softerhardware/Hermes-Lite/rtl/Hermes_Lite_CVA9.v

//
//  Hermes Lite Core Wrapper for BeMicro CV
// 
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
// (C) Steve Haynal KF7O 2014
//

module Hermes_Lite(
	input clk50mhz,
	input exp_present,
	input AD9866clk,
	input clk,
 	input extreset,
	output [7:0] leds,
	output exp_ptt_n,
	output [6:0] userout,
	input [2:0] dipsw,

    input cwkey_i,
    output cwkey_o,
    input ptt_i,

	// AD9866
	output [5:0] ad9866_pga,
`ifdef FULLDUPLEX
	input [5:0] ad9866_rx,
(* useioff = 1 *) output [5:0] ad9866_tx,
	input ad9866_rxsync,
	input ad9866_rxclk,
(* useioff = 1 *) output ad9866_txsync,
	output ad9866_txquietn,
`else
	inout [11:0] ad9866_adio,
	output ad9866_rxen,
	output ad9866_rxclk,
	output ad9866_txen,
	output ad9866_txclk,
`endif
	output ad9866_sclk,
    output ad9866_sdio,
    input  ad9866_sdo,
    output ad9866_sen_n,
    output ad9866_rst_n,
    output ad9866_mode,
   
    // MII Interface
  	output [3:0]PHY_TX,
  	output PHY_TX_EN,              
  	output  PHY_TX_CLOCK_out,           
  	input  [3:0]PHY_RX,     
  	input  RX_DV,                  
  	input  PHY_RX_CLOCK,           
  	output PHY_RESET_N,
	inout  PHY_MDIO,               
	output PHY_MDC,

	//12 bit adc's (ADC78H90CIMT)
	output ADCMOSI,                
	output ADCCLK,
 	input  ADCMISO,
	output nADCCS
);

// PARAMETERS

// Ethernet Interface
// 5c release, 4a testing
parameter MAC = {8'h00,8'h1c,8'hc0,8'ha2,8'h22,8'hdd};
parameter IP = {8'd0,8'd0,8'd0,8'd0};

// Clock Frequency
//parameter CLK_FREQ = 61440000;
parameter CLK_FREQ = 73728000;

// Number of Receivers
parameter NR = 3; // number of receivers to implement

parameter GIGABIT = 1;



// Clocks
wire IF_clk;
wire slowclk;
wire testAD9866clk;
wire AD9866clkX1;
wire IF_locked;
ifclocks_cv ifclocks_cv_inst(
	.refclk(clk),
	.rst(1'b0),
	.outclk_0(IF_clk),
	.outclk_1(testAD9866clk),
	.outclk_2(slowclk),
	.locked(IF_locked)
	);

// PLL clk must me on input 2 or 3
clkmux_cv clkmux (
	.inclk0x(AD9866clk),
	.inclk1x(AD9866clk),
	.inclk2x(testAD9866clk),
	.clkselect({~dipsw[2],1'b0}),
	.outclk(AD9866clkX1)
);

// Hermes Lite Core
hermes_lite_core #(
	.MAC(MAC),
	.IP(IP),
	.CLK_FREQ(CLK_FREQ),
	.NR(NR),
	.GIGABIT(GIGABIT)
	) 

	hermes_lite_core_inst(
	.clk50mhz(clk50mhz),
	.exp_present(dipsw[2]),
	.AD9866clkX1(AD9866clkX1),

	.IF_clk(IF_clk),
	.ad9866spiclk(IF_clk),
	.rstclk(slowclk),
	.EEPROM_clock(slowclk),
	.IF_locked(IF_locked),

 	.extreset(extreset),
	.leds(leds), 
	.exp_ptt_n(exp_ptt_n),
	.userout(userout),
	.dipsw(dipsw),

	.cwkey_i(cwkey_i),
	.cwkey_o(cwkey_o),

	.ptt_i(ptt_i),

	// AD9866
	.ad9866_pga(ad9866_pga),
`ifdef FULLDUPLEX
	.ad9866_tx(ad9866_tx),
	.ad9866_rx(ad9866_rx),
	.ad9866_rxsync(ad9866_rxsync),
	.ad9866_rxclk(ad9866_rxclk),
	.ad9866_txsync(ad9866_txsync),
	.ad9866_txquietn(ad9866_txquietn),
`else
	.ad9866_adio(ad9866_adio),
	.ad9866_rxen(ad9866_rxen),
	.ad9866_rxclk(ad9866_rxclk),
	.ad9866_txen(ad9866_txen),
	.ad9866_txclk(ad9866_txclk),
`endif
	.ad9866_sclk(ad9866_sclk),
    .ad9866_sdio(ad9866_sdio),
    .ad9866_sdo(ad9866_sdo),
    .ad9866_sen_n(ad9866_sen_n),
    .ad9866_rst_n(ad9866_rst_n),
    .ad9866_mode(ad9866_mode),
   
    // MMI Ethernet PHY
  	.PHY_TX(PHY_TX),
  	.PHY_TX_EN(PHY_TX_EN),        
  	.PHY_TX_CLOCK(1'b0),
  	.PHY_TX_CLOCK_out(PHY_TX_CLOCK_out),
  	.PHY_RX(PHY_RX),     
  	.RX_DV(RX_DV),
  	.PHY_RX_CLOCK(PHY_RX_CLOCK),         
  	.PHY_RESET_N(PHY_RESET_N),
	.PHY_MDIO(PHY_MDIO),             
	.PHY_MDC(PHY_MDC),

	//12 bit adc's (ADC78H90CIMT)
	.ADCMOSI(ADCMOSI),                
	.ADCCLK(ADCCLK),
 	.ADCMISO(ADCMISO),
	.nADCCS(nADCCS)	
);             

//reg clkcheck;
//always @(negedge rmii_osc)
//	clkcheck <= PHY_TX_CLOCK ^ PHY_RX_CLOCK;

//assign leds = { ileds[7:1],~clkcheck };

endmodule 
