softerhardware/Hermes-Lite/rtl/receiver.v

/*
--------------------------------------------------------------------------------
This library is free software; you can redistribute it and/or
modify it under the terms of the GNU Library General Public
License as published by the Free Software Foundation; either
version 2 of the License, or (at your option) any later version.
This library is distributed in the hope that it will be useful,
but WITHOUT ANY WARRANTY; without even the implied warranty of
MERCHANTABILITY or FITNESS FOR A PARTICULAR PURPOSE.  See the GNU
Library General Public License for more details.
You should have received a copy of the GNU Library General Public
License along with this library; if not, write to the
Free Software Foundation, Inc., 51 Franklin St, Fifth Floor,
Boston, MA  02110-1301, USA.
--------------------------------------------------------------------------------
*/


//------------------------------------------------------------------------------
//           Copyright (c) 2008 Alex Shovkoplyas, VE3NEA
//------------------------------------------------------------------------------

//------------------------------------------------------------------------------
//           Copyright (c) 2013 Phil Harman, VK6APH 
//------------------------------------------------------------------------------

// 2013 Jan 26 - varcic now accepts 2...40 as decimation and CFIR
//               replaced with Polyphase FIR - VK6APH

// 2015 Jan 31 - updated for Hermes-Lite 12bit Steve Haynal KF7O

module receiver(
  input clock,                  //61.44 MHz
  input [5:0] rate,             //48k....384k
  input [31:0] frequency,
  output out_strobe,
  input signed [11:0] in_data,
  output [23:0] out_data_I,
  output [23:0] out_data_Q,
  output signed [17:0] cordic_outdata_I,	// make cordic data available for VNA_SCAN_FPGA
  output signed [17:0] cordic_outdata_Q
  );

  parameter CICRATE;

// gain adjustment, Hermes reduced by 6dB to match previous receiver code.
// Hermes-Lite gain reduced to calibrate QtRadio
wire signed [23:0] out_data_I2;
wire signed [23:0] out_data_Q2;
assign out_data_I = out_data_I2; //>>> 3);
assign out_data_Q = out_data_Q2; //>>> 3);


//------------------------------------------------------------------------------
//                               cordic
//------------------------------------------------------------------------------

cordic cordic_inst(
  .clock(clock),
  .in_data(in_data),             //12 bit 
  .frequency(frequency),         //32 bit
  .out_data_I(cordic_outdata_I), //18 bit
  .out_data_Q(cordic_outdata_Q)
  );

  
// Receive CIC filters followed by FIR filter
wire decimA_avail, decimB_avail;
wire signed [13:0] decimA_real, decimA_imag;
wire signed [15:0] decimB_real, decimB_imag;

localparam VARCICWIDTH = (CICRATE == 10) ? 34 : (CICRATE == 13) ? 34 : (CICRATE == 5) ? 41 : 37; // Last is default rate of 8
localparam ACCWIDTH = (CICRATE == 10) ? 28 : (CICRATE == 13) ? 30 : (CICRATE == 5) ? 25 : 27; // Last is default rate of 8


// CIC filter 
//I channel
cic #(.STAGES(3), .DECIMATION(CICRATE), .IN_WIDTH(18), .ACC_WIDTH(ACCWIDTH), .OUT_WIDTH(14))      
  cic_inst_I2(
    .clock(clock),
    .in_strobe(1'b1),
    .out_strobe(decimA_avail),
    .in_data(cordic_outdata_I),
    .out_data(decimA_real)
    );

//Q channel
cic #(.STAGES(3), .DECIMATION(CICRATE), .IN_WIDTH(18), .ACC_WIDTH(ACCWIDTH), .OUT_WIDTH(14))  
  cic_inst_Q2(
    .clock(clock),
    .in_strobe(1'b1),
    .out_strobe(),
    .in_data(cordic_outdata_Q),
    .out_data(decimA_imag)
    );


//  Variable CIC filter - in width = out width = 14 bits, decimation rate = 2 to 16 
//I channel
varcic #(.STAGES(5), .IN_WIDTH(14), .ACC_WIDTH(VARCICWIDTH), .OUT_WIDTH(16), .CICRATE(CICRATE))
  varcic_inst_I1(
    .clock(clock),
    .in_strobe(decimA_avail),
    .decimation(rate),
    .out_strobe(decimB_avail),
    .in_data(decimA_real),
    .out_data(decimB_real)
    );

//Q channel
varcic #(.STAGES(5), .IN_WIDTH(14), .ACC_WIDTH(VARCICWIDTH), .OUT_WIDTH(16), .CICRATE(CICRATE))
  varcic_inst_Q1(
    .clock(clock),
    .in_strobe(decimA_avail),
    .decimation(rate),
    .out_strobe(),
    .in_data(decimA_imag),
    .out_data(decimB_imag)
    );
				
firX8R8 fir2 (clock, decimB_avail, {{2{decimB_real[15]}},decimB_real}, {{2{decimB_imag[15]}},decimB_imag}, out_strobe, out_data_I2, out_data_Q2);

endmodule
