softerhardware/Hermes-Lite/rtl/clkmux_cv/clkmux_cv_inst.v

	clkmux_cv u0 (
		.inclk2x   (<connected-to-inclk2x>),   //  altclkctrl_input.inclk2x
		.inclk1x   (<connected-to-inclk1x>),   //                  .inclk1x
		.inclk0x   (<connected-to-inclk0x>),   //                  .inclk0x
		.clkselect (<connected-to-clkselect>), //                  .clkselect
		.outclk    (<connected-to-outclk>)     // altclkctrl_output.outclk
	);
