softerhardware/Hermes-Lite/rtl/clkmux_sdk/clkmux_sdk_bb.v

module clkmux_sdk (
	inclk3x,
	inclk2x,
	inclk1x,
	inclk0x,
	clkselect,
	outclk);	

	input		inclk3x;
	input		inclk2x;
	input		inclk1x;
	input		inclk0x;
	input	[1:0]	clkselect;
	output		outclk;
endmodule
